Elektrospy/PowerSupplyMonitor/PowerSupplyMonitorFirmware/i2cNode.h

// i2cnode.h
#ifndef I2CNODE_H
#define I2CNODE_H
#include <Wire.h>
#include <TwoWireMux.h>
#include <TI_TCA9548A.h>
#include <Adafruit_ADS1015.h>

class i2cNode {
	
public:
	i2cNode();
	i2cNode(TI_TCA9548A *tca, uint8_t tcaPort);
	~i2cNode();
	float getAmpereForOutput(uint8_t);

private:
	Adafruit_ADS1015 _ads;
	uint16_t _numberOfProbes;
	uint16_t _adcList[4];
	uint16_t _adcAvgList[4];
	uint8_t _numberOfAdcs;
	uint8_t _tcaPort;
	TI_TCA9548A *_tca;

	void _init();

	void _getValuesRaw();
	float _calculateAmpereAverage(uint16_t);
};

#endif
